keener2u/CoinPCB/pics/coin3d-v0.1.png

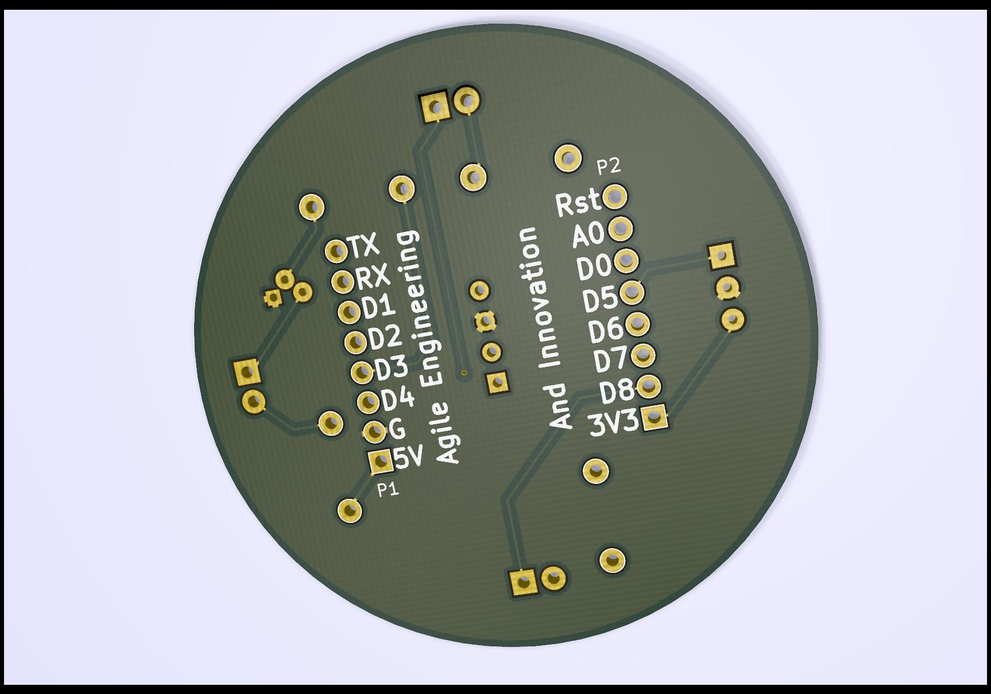
pics/coin3d-v0.1.png
