keener2u/CoinPCB/pics/coin3d-v0.2-draft.png

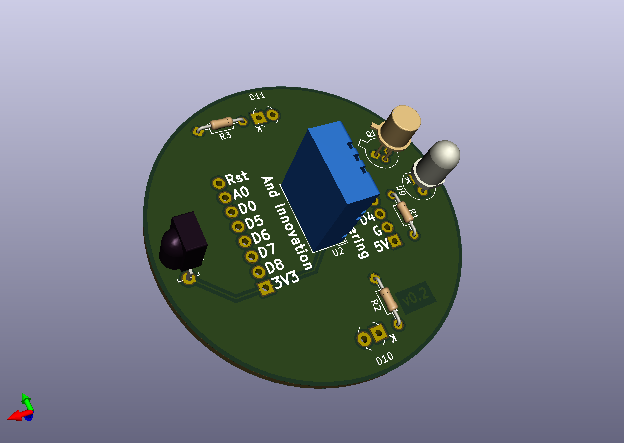
pics/coin3d-v0.2-draft.png
