keener2u/CoinPCB/pics/coin3d_2-v0.1.png

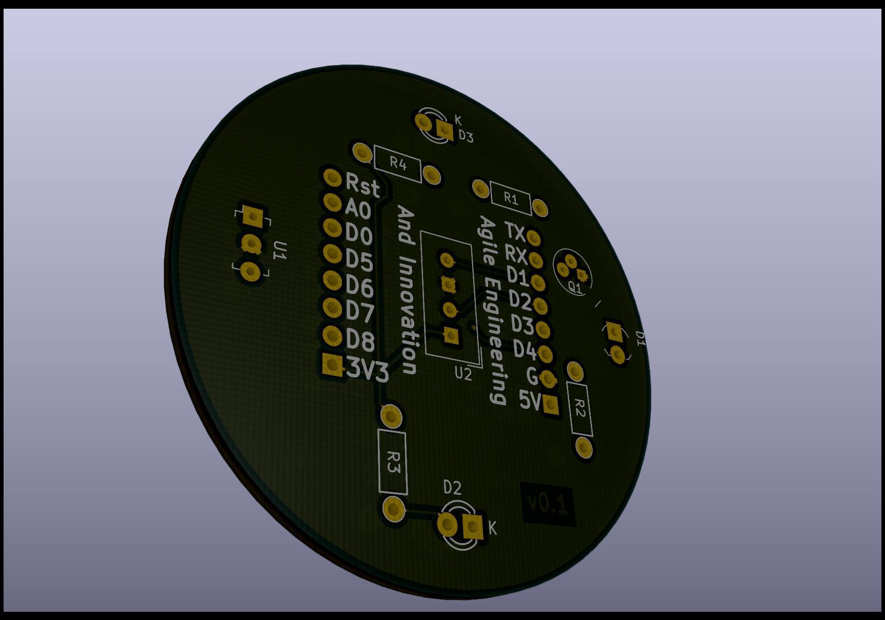
pics/coin3d_2-v0.1.png
