keener2u/CoinPCB/pics/coinPicture-1.5inch-beta.jpg

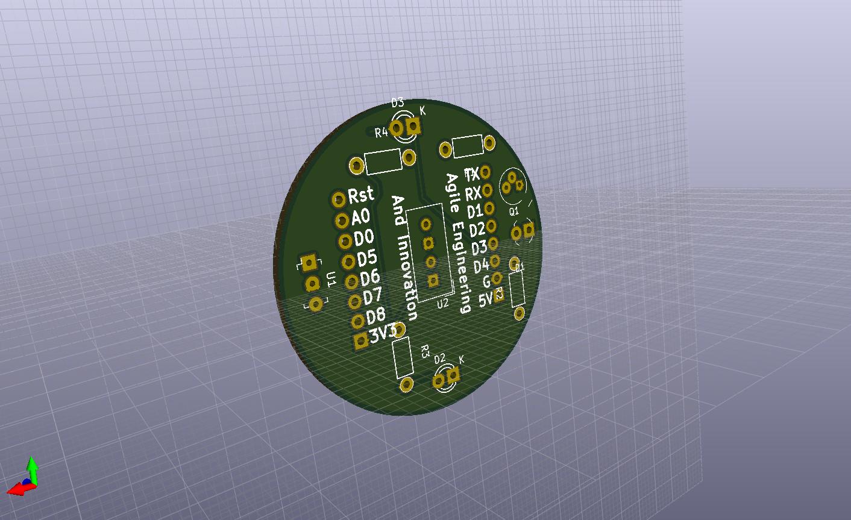
pics/coinPicture-1.5inch-beta.jpg
