keener2u/CoinPCB/pics/build-steps/Step3.JPG

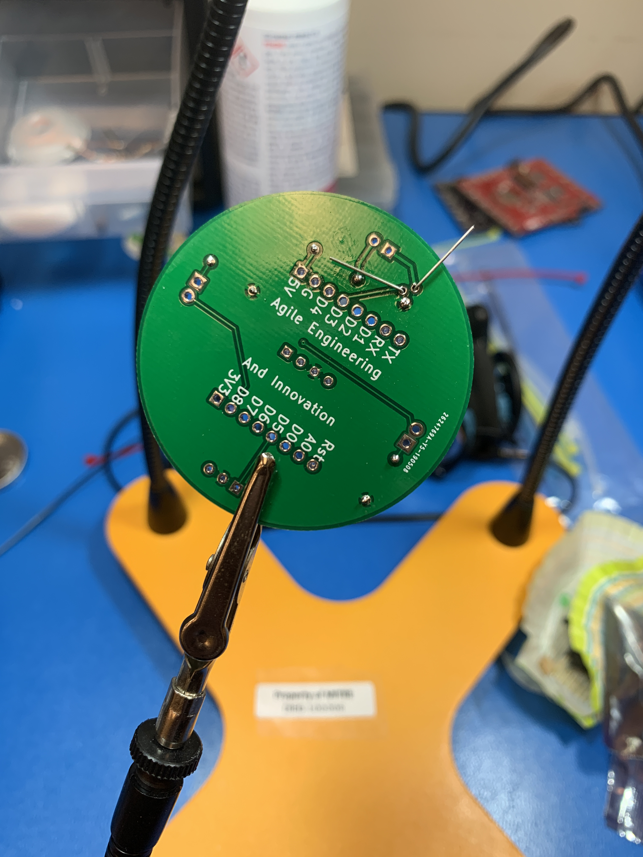
pics/build-steps/Step3.JPG
