keener2u/CoinPCB/pics/build-steps/Step4.JPG

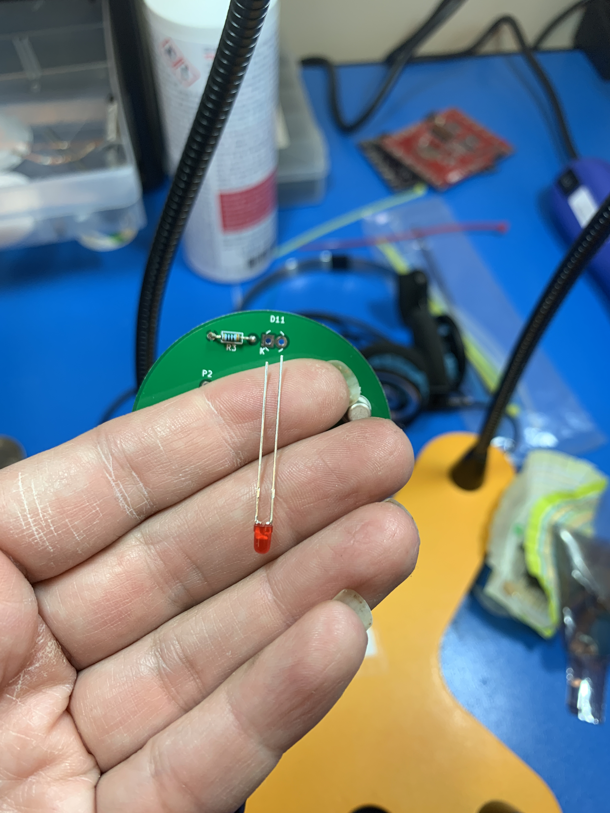
pics/build-steps/Step4.JPG
