keener2u/CoinPCB/pics/build-steps/Step6.JPG

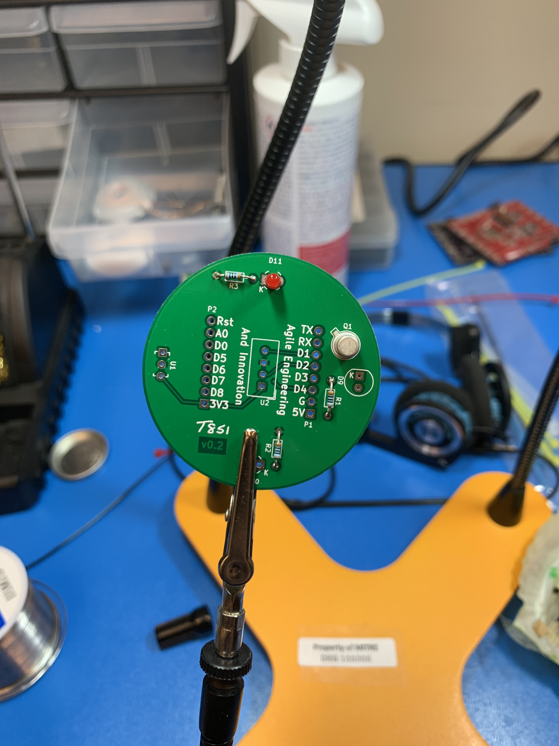
pics/build-steps/Step6.JPG
