keener2u/CoinPCB/pics/build-steps/Step8.1.JPG

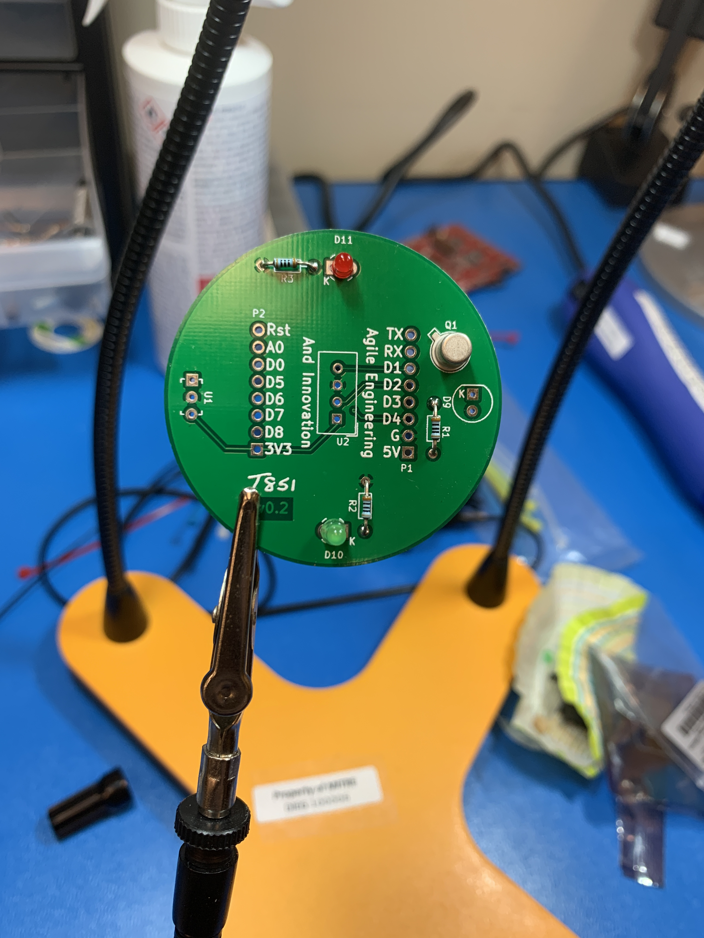
pics/build-steps/Step8.1.JPG
