keener2u/CoinPCB/pics/build-steps/Step9.JPG

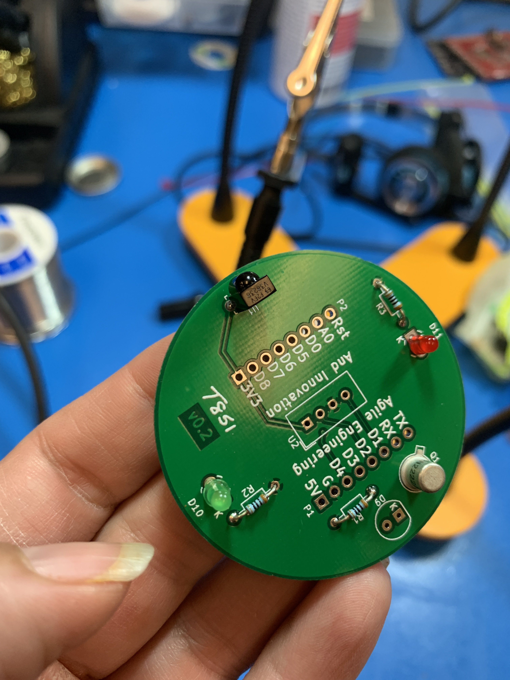
pics/build-steps/Step9.JPG
