keener2u/CoinPCB/pics/build-steps/Step10.JPG

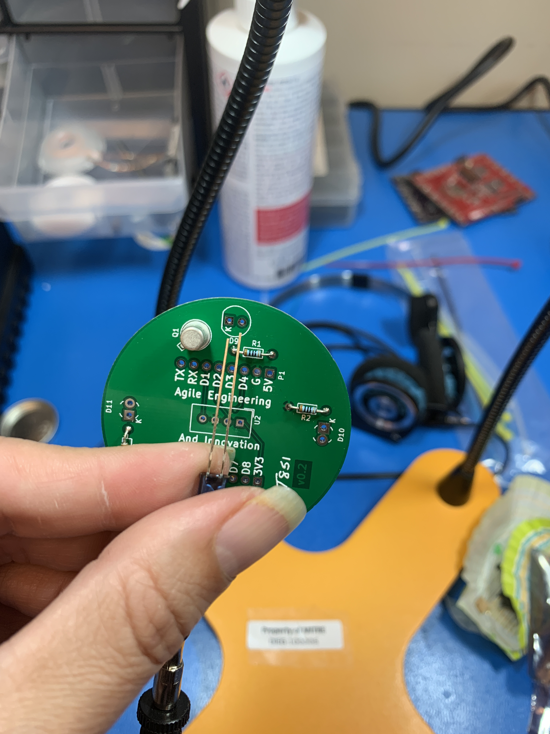
pics/build-steps/Step10.JPG
