keener2u/CoinPCB/pics/build-steps/Step13.JPG

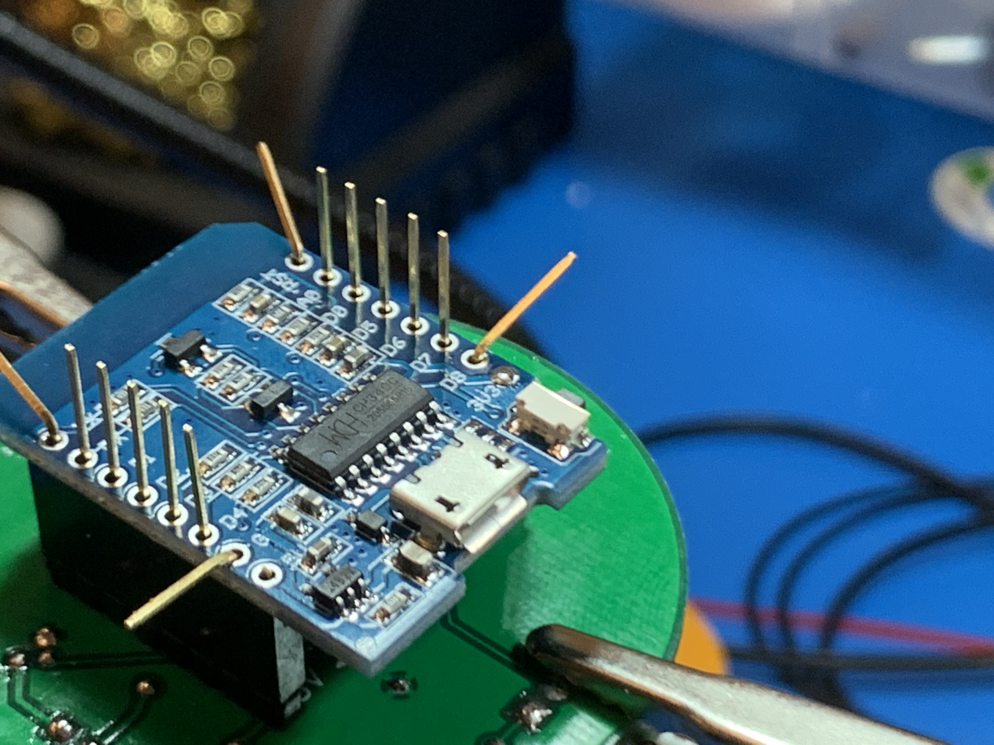
pics/build-steps/Step13.JPG
