keener2u/CoinPCB/pics/build-steps/Step14.JPG

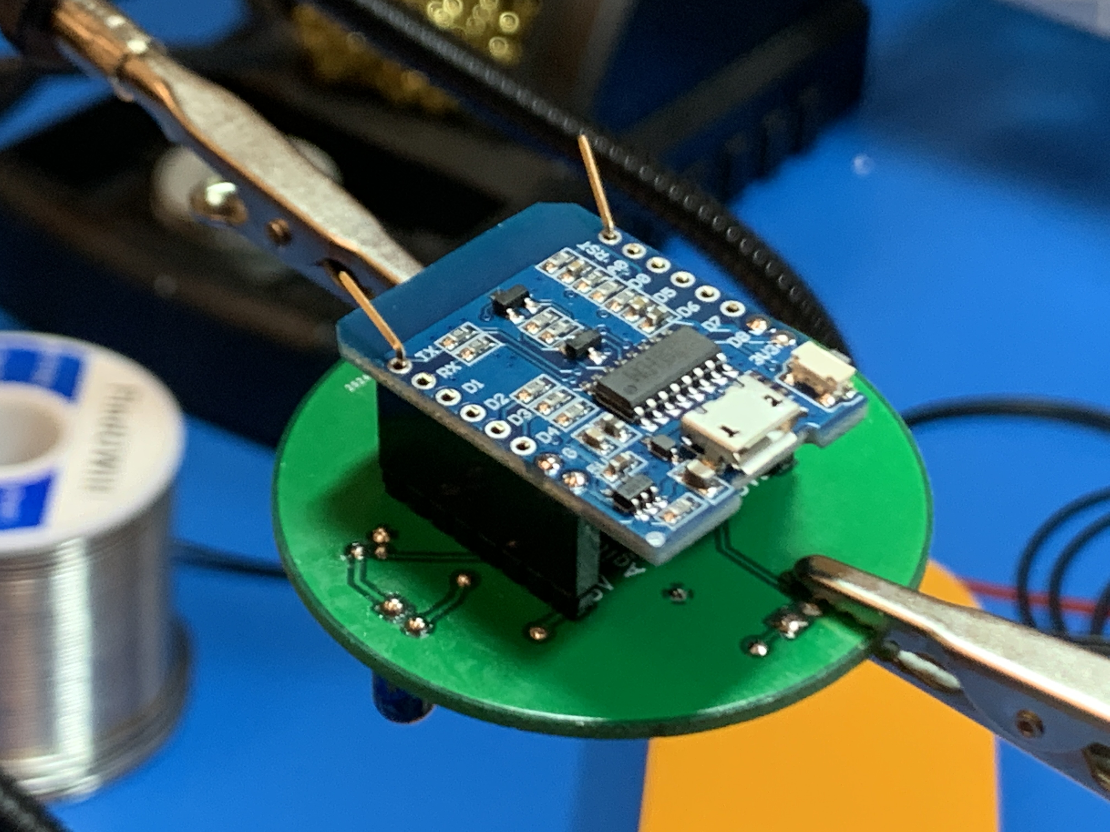
pics/build-steps/Step14.JPG
