keener2u/CoinPCB/pics/build-steps/Step1.JPG

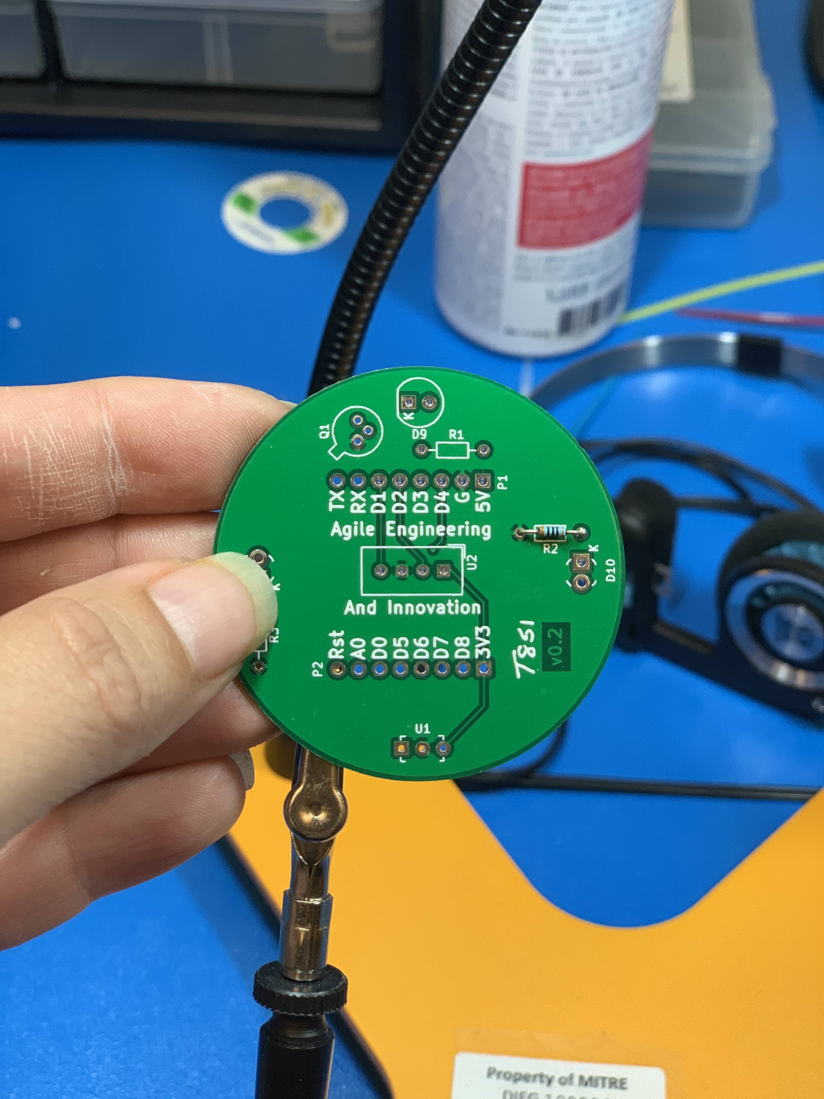
pics/build-steps/Step1.JPG
