keener2u/CoinPCB/pics/build-steps/Step5.JPG

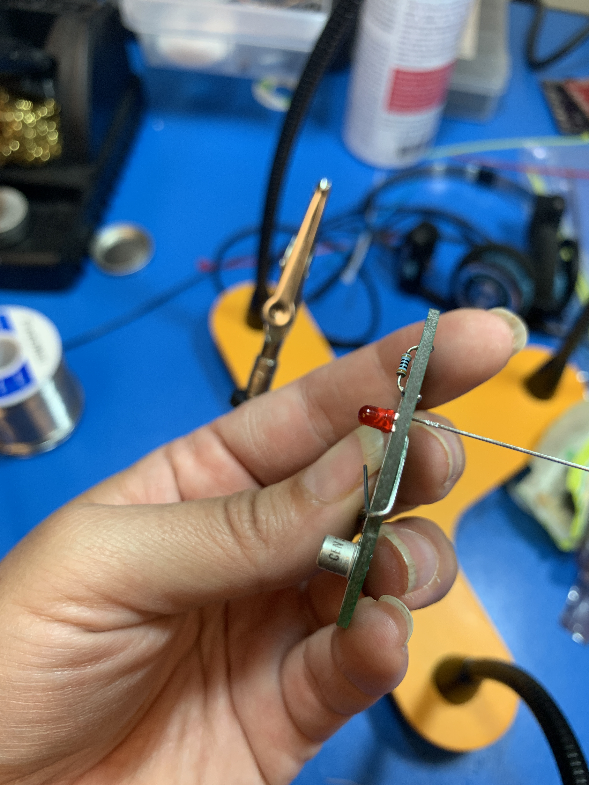
pics/build-steps/Step5.JPG
