keener2u/CoinPCB/pics/build-steps/Step8.JPG

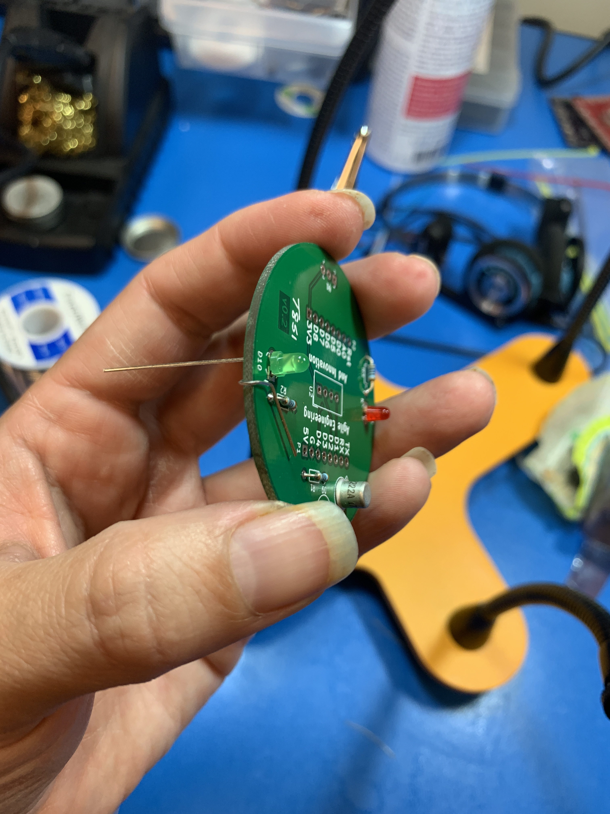
pics/build-steps/Step8.JPG
